mjgardes/mppt3/panel_sim.asc

D1: zener; BZX84C15L
D2: zener; BZX84C15L
D3: zener; BZX84C15L
I1: current; .3
R1: res; 1000
R2: res; 3
V1: voltage; PWL(0 -1 1 48)
Named nets: 0
.tran 1
