mjgardes/mppt3/weinberg.asc

C1: cap; 100µF; Rser=0
C2: cap; 10µF
C3: cap; .1µF; Rser=.3
C4: cap; .1µF; Rser=.3
D1: zener; BZX84C15L
D2: diode; MURS120
D3: diode; MURS120
D5: zener; BZX84C15L
D6: zener; BZX84C15L
I2: current; .3
L1: ind2; 4.54mH; Rser=.2
L2: ind2; 4.54mH; Rser=.2
L3: ind2; 4.54mH; Rser=.2
L4: ind2; 4.54mH; Rser=.2
M1: nmos; BSC16DN25NS3
M2: nmos; BSC16DN25NS3
R1: res; 3R
R2: res; 1000
R3: res; 3
R4: res; 1
V1: voltage; PULSE(0 12 {t0/2} {slew} {slew} {tOn} {t0})
V2: voltage; PULSE(0 12 0 {slew} {slew} {tOn} {t0})
V4: voltage; 13.5; Rser=.1
Named nets: 0
K2 L3 L4 .99
K1 L1 L2 .99
.tran 0 10ms 3ms
.param f0 150k
.step param duty 25 26 .2
.param slew 5n
.param t0 {1/{f0}}
.param tOn {{t0}*{{duty}/100}-{2*{slew}}}
